udaysolanki4/Hand-Gesture/major1_tx.brd.png

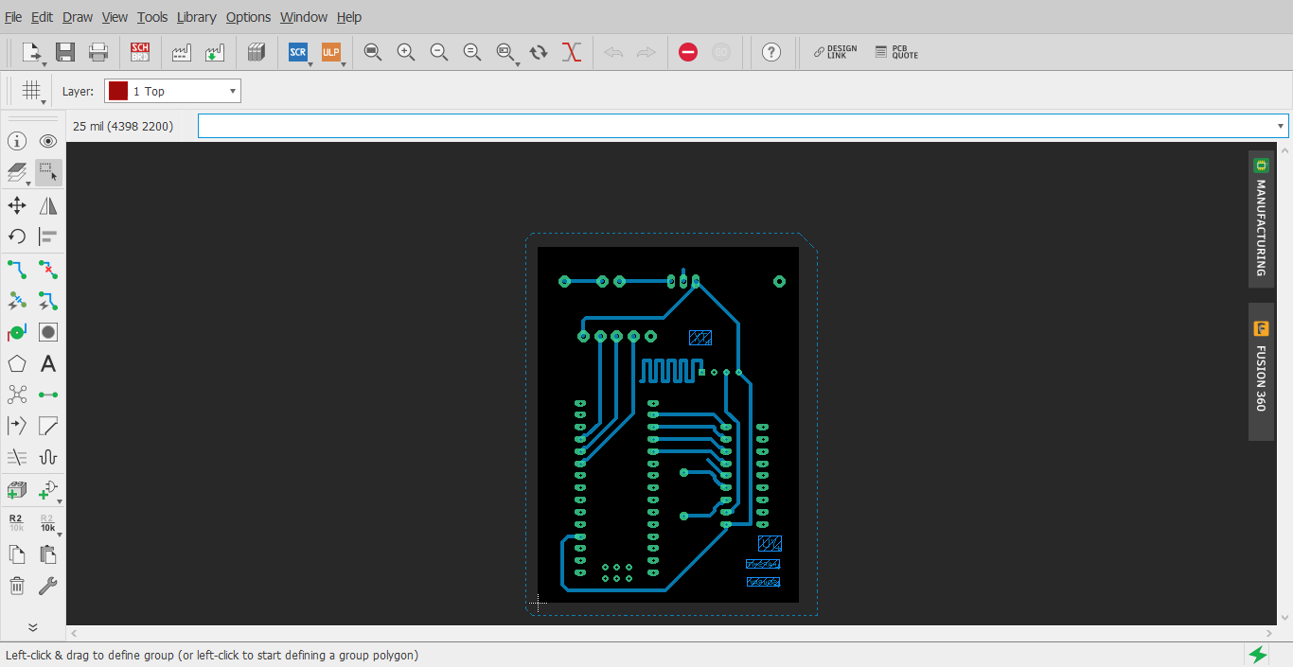
major1_tx.brd.png
