udaysolanki4/Hand-Gesture/TxCapture.JPG

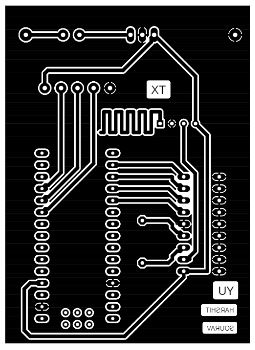
TxCapture.JPG
